danjulio/gCore/Firmware/gcore_ctrl/src/adc.c

/*
 * adc.c
 *
 * ADC Measurement module
 *  Implement an interrupt-driven sampling system for USB input voltage and current, battery
 *  voltage, load current and internal temp.  TIMER0 IRQ triggers ADC readings.  ADC IRQ used
 *  to update values.
 *
 * Functions:
 *  1. Initialization
 *    - Initialize filter used for noisy voltage and current measurements
 *    - Read temp - initialize averaging array
 *    - Enable timer + adc interrupts
 *  2. Digitally filtered measurements for voltage and current to handle varying values that
 *     make it through the external low-pass hardware filters.  Measurements made for each
 *     voltage and current channel at approximately 1 kHz.
 *  3. Skew TIMER0 reload value back and forth around the center sample rate to jitter ADC sampling.
 *  4. Temperature sensor measurements every second and averaging over a several second period.
 *  5. Value access routines for other modules.
 *
 * Copyright (c) 2021-2022 danjuliodesigns, LLC.  All rights reserved.
 *
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
 */
#include "intrins.h"
#include "adc.h"
#include "config.h"
#include "smbus.h"


//-----------------------------------------------------------------------------
// Module constants
//-----------------------------------------------------------------------------

// ADC Inputs
#define _ADC_VU_CH 1
#define _ADC_IU_CH 2
#define _ADC_VB_CH 3
#define _ADC_IL_CH 4
#define _ADC_TI_CH 27

// Timer0 reload min/max counts
//  Chosen to allow the sample point to skew around the entire PWM period to
//  more accurately measure a varying signal during that time.
//    - Skew around timer 0 reload base value of 0x80 (~250 uSec/sample)
//    - Timer 0 count = 1.96 uSec
//    - PWM Period = 41.8 uSec
//    => Minimum of 41.8/1.96 = ~21.3 counts
//  However the following values were empirically found to work well with
//  the selected filter constant K.
#define _ADC_TH0_MIN 0x77
#define _ADC_TH0_MAX 0x88



//-----------------------------------------------------------------------------
// Voltage and Current ADC Count to output lookup tables
//-----------------------------------------------------------------------------

// mV = (ADC_COUNT * VREF * V_SF) / 1023 = (ADC_COUNT * 1250 * 5.02) / 1023
code const uint16_t adc_2_mv[] = {
	0, 6, 12, 18, 25, 31, 37, 43, 49, 55, 61, 67, 74, 80, 86, 92,
	98, 104, 110, 117, 123, 129, 135, 141, 147, 153, 159, 166, 172, 178, 184, 190,
	196, 202, 209, 215, 221, 227, 233, 239, 245, 251, 258, 264, 270, 276, 282, 288,
	294, 301, 307, 313, 319, 325, 331, 337, 343, 350, 356, 362, 368, 374, 380, 386,
	393, 399, 405, 411, 417, 423, 429, 436, 442, 448, 454, 460, 466, 472, 478, 485,
	491, 497, 503, 509, 515, 521, 528, 534, 540, 546, 552, 558, 564, 570, 577, 583,
	589, 595, 601, 607, 613, 620, 626, 632, 638, 644, 650, 656, 662, 669, 675, 681,
	687, 693, 699, 705, 712, 718, 724, 730, 736, 742, 748, 754, 761, 767, 773, 779,
	785, 791, 797, 804, 810, 816, 822, 828, 834, 840, 846, 853, 859, 865, 871, 877,
	883, 889, 896, 902, 908, 914, 920, 926, 932, 938, 945, 951, 957, 963, 969, 975,
	981, 988, 994, 1000, 1006, 1012, 1018, 1024, 1030, 1037, 1043, 1049, 1055, 1061, 1067, 1073,
	1080, 1086, 1092, 1098, 1104, 1110, 1116, 1123, 1129, 1135, 1141, 1147, 1153, 1159, 1165, 1172,
	1178, 1184, 1190, 1196, 1202, 1208, 1215, 1221, 1227, 1233, 1239, 1245, 1251, 1257, 1264, 1270,
	1276, 1282, 1288, 1294, 1300, 1307, 1313, 1319, 1325, 1331, 1337, 1343, 1349, 1356, 1362, 1368,
	1374, 1380, 1386, 1392, 1399, 1405, 1411, 1417, 1423, 1429, 1435, 1441, 1448, 1454, 1460, 1466,
	1472, 1478, 1484, 1491, 1497, 1503, 1509, 1515, 1521, 1527, 1533, 1540, 1546, 1552, 1558, 1564,
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
	430, 431, 433, 434, 435, 436, 437, 439, 440, 441, 442, 444, 445, 446, 447, 448,
	450, 451, 452, 453, 455, 456, 457, 458, 459, 461, 462, 463, 464, 466, 467, 468,
	469, 470, 472, 473, 474, 475, 477, 478, 479, 480, 481, 483, 484, 485, 486, 488,
	489, 490, 491, 492, 494, 495, 496, 497, 499, 500, 501, 502, 503, 505, 506, 507,
	508, 510, 511, 512, 513, 514, 516, 517, 518, 519, 521, 522, 523, 524, 525, 527,
	528, 529, 530, 532, 533, 534, 535, 536, 538, 539, 540, 541, 543, 544, 545, 546,
	547, 549, 550, 551, 552, 554, 555, 556, 557, 558, 560, 561, 562, 563, 565, 566,
	567, 568, 569, 571, 572, 573, 574, 576, 577, 578, 579, 580, 582, 583, 584, 585,
	587, 588, 589, 590, 591, 593, 594, 595, 596, 598, 599, 600, 601, 602, 604, 605,
	606, 607, 609, 610, 611, 612, 613, 615, 616, 617, 618, 620, 621, 622, 623, 624,
	626, 627, 628, 629, 630, 632, 633, 634, 635, 637, 638, 639, 640, 641, 643, 644,
	645, 646, 648, 649, 650, 651, 652, 654, 655, 656, 657, 659, 660, 661, 662, 663,
	665, 666, 667, 668, 670, 671, 672, 673, 674, 676, 677, 678, 679, 681, 682, 683,
	684, 685, 687, 688, 689, 690, 692, 693, 694, 695, 696, 698, 699, 700, 701, 703,
	704, 705, 706, 707, 709, 710, 711, 712, 714, 715, 716, 717, 718, 720, 721, 722,
	723, 725, 726, 727, 728, 729, 731, 732, 733, 734, 736, 737, 738, 739, 740, 742,
	743, 744, 745, 747, 748, 749, 750, 751, 753, 754, 755, 756, 758, 759, 760, 761,
	762, 764, 765, 766, 767, 769, 770, 771, 772, 773, 775, 776, 777, 778, 780, 781,
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
};




//-----------------------------------------------------------------------------
// Variables
//-----------------------------------------------------------------------------

// Filtered measurement variables
static volatile uint32_t SI_SEG_IDATA adcFilterSum[4];

// Temperature measurement variables
static volatile uint16_t SI_SEG_IDATA adcTempAvgArray[ADC_NUM_TEMP_SMPLS];
static volatile uint8_t SI_SEG_IDATA adcTempAvgIndex;

// State management variables
static volatile uint8_t adcMeasIndex;	     // Current index being measured
static volatile uint8_t adcStoredMeasIndex;  // Index to restore after temperature measurement "interruption"
static volatile uint16_t adcTempMeasCount;	 // Counts down series between temperature measurements (slow)

// Timer 0 sample control
static volatile uint8_t adcTimer0Reload;
static volatile bit adcTimer0ReloadInc;



//-----------------------------------------------------------------------------
// Forward declarations for internal functions
//-----------------------------------------------------------------------------
static void _ADC_DelayMsec(uint8_t mSec);
static uint16_t _ADC_GetSingleReading(uint8_t adcChannel);
static void _ADC_PushFilteredVal(uint16_t val, uint8_t index);
static void _ADC_PushTemp(uint16_t val);
static int16_t _adc2IntT10(uint16_t adcVal);



//-----------------------------------------------------------------------------
// API Routines
//-----------------------------------------------------------------------------
void ADC_Init()
{
	uint8_t i;
	uint16_t v;

	// Make sure ADC Interrupts are disabled so ISRs don't fire while we're initializing
	ADC_DIS_INT();

	// Delay to allow voltages to stabilize
	_ADC_DelayMsec(50);

	// Initialize variables
	adcMeasIndex = 0;
	adcTempMeasCount = ADC_TEMP_EVAL_COUNT;
	adcTimer0Reload = 0x80;
	adcTimer0ReloadInc = 1;

	// Setup the filtered ADC value filters
	v = _ADC_GetSingleReading(_ADC_VU_CH);
	adcFilterSum[ADC_MEAS_VU_INDEX] = (v << ADC_V_FILTER_SHIFT);
	SMB_SetVU(adc_2_mv[v]);
	v = _ADC_GetSingleReading(_ADC_IU_CH);
	adcFilterSum[ADC_MEAS_IU_INDEX] = (v << ADC_I_FILTER_SHIFT);
	SMB_SetIU(adc_2_ma[v]);
	v = _ADC_GetSingleReading(_ADC_VB_CH);
	adcFilterSum[ADC_MEAS_VB_INDEX] = (v << ADC_V_FILTER_SHIFT);
	SMB_SetVB(adc_2_mv[v]);
	v = _ADC_GetSingleReading(_ADC_IL_CH);
	adcFilterSum[ADC_MEAS_IL_INDEX] = (v << ADC_I_FILTER_SHIFT);
	SMB_SetIL(adc_2_ma[v]);

	// Load the temperature averaging arrays
	v = _ADC_GetSingleReading(_ADC_TI_CH);
	for (i=0; i<ADC_NUM_TEMP_SMPLS-1; i++) {
		_ADC_PushTemp(v);
	}

	// Configure the ADC input for the initial reading
	ADC0MX = _ADC_VU_CH;

	// Enable Timer0
	TCON_TR0 = 1;

	// Enable ADC Interrupts
	ADC_EN_INT();
}



//-----------------------------------------------------------------------------
// Interrupt Handlers
//-----------------------------------------------------------------------------
// TIMER0_IRQ requires ~1.3 - 1.5 uSec typically
SI_INTERRUPT (TIMER0_ISR, TIMER0_IRQn)
{
	// Trigger an ADC reading
	ADC0CN0_ADBUSY = 1;

	// Update the reload value to skew the period between samples
	if (adcTimer0ReloadInc == 1) {
		if (++adcTimer0Reload == _ADC_TH0_MAX) {
			adcTimer0ReloadInc = 0;
		}
	} else {
		if (--adcTimer0Reload == _ADC_TH0_MIN) {
			adcTimer0ReloadInc = 1;
		}
	}
	TH0 = adcTimer0Reload;

	// Clear TCON::TF0 (Timer 0 Overflow Flag) - done by HW on entry to ISR
}


// ADC0E0C_IRQ requires ~22-27 uSec
// (greater if blocked while writing to SMBus, typ up to 400 uSec if reading time)
SI_INTERRUPT (ADC0EOC_ISR, ADC0EOC_IRQn)
{
	// Store the ADC result
	if (adcMeasIndex <= ADC_MEAS_IL_INDEX) {
		_ADC_PushFilteredVal(ADC0, adcMeasIndex);
	} else {
		// Temperature
		_ADC_PushTemp(ADC0);
	}

	// Setup the next ADC reading
	if (adcMeasIndex == ADC_MEAS_T_INDEX) {
		// Restore normal operation
		adcMeasIndex = adcStoredMeasIndex;
	} else {
		// Setup for next channel
		if (++adcMeasIndex > ADC_MEAS_IL_INDEX) {
			adcMeasIndex = 0;
		}
		if (--adcTempMeasCount == 0) {
			// Setup special case of occasional temperature measurement
			adcTempMeasCount = ADC_TEMP_EVAL_COUNT; // Reset temperature timer
			adcStoredMeasIndex = adcMeasIndex;      // Save current normal channel to restore
			adcMeasIndex = ADC_MEAS_T_INDEX;        // Internal temperature sensor
		}
	}

	// Configure the ADC input for the next reading
	switch (adcMeasIndex) {
	case ADC_MEAS_VU_INDEX:
		ADC0MX = _ADC_VU_CH;
		break;
	case ADC_MEAS_IU_INDEX:
		ADC0MX = _ADC_IU_CH;
		break;
	case ADC_MEAS_VB_INDEX:
		ADC0MX = _ADC_VB_CH;
		break;
	case ADC_MEAS_IL_INDEX:
		ADC0MX = _ADC_IL_CH;
		break;
	default:
		ADC0MX = _ADC_TI_CH;
		break;
	}

	// Clear ADC0CN0::ADINT (Conversion Complete Interrupt Flag)
	ADC0CN0_ADINT = 0;
}



//-----------------------------------------------------------------------------
// Internal Routines
//-----------------------------------------------------------------------------

// Delay function designed for use during initialization - ADC/Timer0 interrupts must be disabled
void _ADC_DelayMsec(uint8_t mSec)
{
	uint8_t i;

	// Uses Timer0 overflow at ~250 uSec
	TCON_TF0 = 0;  // Clear overflow flag
	TL0 = TH0;     // Manually set timer for first time
	TCON_TR0 = 1;  // Enable Timer 0
	while (mSec--) {
		for (i=0; i<4; i++) {
			// Spin until timer overflows
			while (TCON_TF0 != 1) {};

			// Reset for next period
			TCON_TF0 = 0;
		}
	}

	// Disable Timer 0
	TCON_TR0 = 0;
	TCON_TF0 = 0;
}


// Single ADC measurement - ADC Interrupts must be disabled
uint16_t _ADC_GetSingleReading(uint8_t adcChannel)
{
	// Set the ADC Channel
	ADC0MX = adcChannel;

	// Wait >5 uSec for input to settle
	_ADC_DelayMsec(10);

	// Trigger ADC
	ADC0CN0_ADINT = 0;
	ADC0CN0_ADBUSY = 1;

	// Wait for ADC to finish
	while (ADC0CN0_ADINT != 1) {};
	ADC0CN0_ADINT = 0;

	return(ADC0);
}


void _ADC_PushFilteredVal(uint16_t val, uint8_t index)
{
	uint16_t v;

	// Even indices are voltage, odd are current
	if (index & 0x01) {
		// Update current filter with current sample
		adcFilterSum[index] = adcFilterSum[index] - (adcFilterSum[index] >> ADC_I_FILTER_SHIFT) + val;

		// Scale for unity gain
		v = adcFilterSum[index] >> ADC_I_FILTER_SHIFT;

		// Push value into SMBUS register
		if (index & 0x02) {
			SMB_SetIL(adc_2_ma[v]);
		} else {
			SMB_SetIU(adc_2_ma[v]);
		}
	} else {
		// Update current filter with current sample
		adcFilterSum[index] = adcFilterSum[index] - (adcFilterSum[index] >> ADC_V_FILTER_SHIFT) + val;

		// Scale for unity gain
		v = adcFilterSum[index] >> ADC_V_FILTER_SHIFT;

		// Push value into SMBUS register
		if (index & 0x02) {
			SMB_SetVB(adc_2_mv[v]);
		} else {
			SMB_SetVU(adc_2_mv[v]);
		}
	}
}


void _ADC_PushTemp(uint16_t val)
{
	uint8_t i;
	uint16_t tempAvgAdcVal = 0;

	// Push current value
	adcTempAvgArray[adcTempAvgIndex] = val;
	if (++adcTempAvgIndex == ADC_NUM_TEMP_SMPLS) adcTempAvgIndex = 0;

	// Compute current averaged ADC value
	tempAvgAdcVal = 0;
	for (i=0; i<ADC_NUM_TEMP_SMPLS; i++) {
		tempAvgAdcVal += adcTempAvgArray[i];
	}

	// Round up the pre-divided value if necessary and then scale to divide
	if (tempAvgAdcVal & ADC_TEMP_RND_MASK) {
		// Round up unshifted sum
		tempAvgAdcVal += ADC_TEMP_RND_MASK;
	}
	tempAvgAdcVal = tempAvgAdcVal >> ADC_TEMP_SHIFT;

	// Push value into SMBUS
	SMB_SetTemp(_adc2IntT10(tempAvgAdcVal));
}


// Return temp in units of C * 10
//
// Internal Temperature Sensor spec says slope is 3.4 mV/C and a 10-bit
// measurement for each device is held in the TOFF register (measured
// at 25C).  An offset for 0C can be calculated by subtracting the
// computed ADC count for 25 degrees C from the TOFF register and
// scaling to 10-bits.
int16_t _adc2IntT10(uint16_t adcVal)
{
	int32_t t;

	// Offset for 0-degree with internal calibration offset
	//   - Offset @ 0C is 940 mV nominal (10-bit ADC count = (940/ADC_VREF_MV)*1023 = 769 ideal
	//   - {TOFFH[7:0], TOFFL[7:6]} contain 10-bit calibrated offset voltage
	//   - Adjust ADC count to 0-degrees with calibration: adcVal - 769 - TOFF
	//
	//t = 961620 / ADC_VREF_MV;
	//t = (int32_t) adcVal - t;
	t = (int32_t) adcVal - 769;
	t = t - (((int32_t) TOFFH << 2) | ((int32_t) TOFFL >> 6));

	// Compute temperature
	//   T_C_10 = (100*ADC_CAL_MV*ADC_VREF_MV)/(1023 * 34)
	t = t * ADC_VREF_MV * 100;
	t = t / 34782;

	return (t);
}
