danjulio/gCore/Arduino/gCore/src/gCore_ILI9488.h

/*
 * Adafruit GFX compatible LCD driver library for danjuliodesigns, LLC gCore
 * development board. Supports 16-bit colors natively.
 *
 * You must also include the Adafruit_GFX library that can be downloaded
 * from https://github/adafruit/Adafruit_GFX.  Thanks to Limor Fried/Ladyada 
 * at Adafruit Industries for all her hard work on these libraries.
 *
 * Written by Dan Julio
 *
 * Copyright 2021 danjuliodesigns, LLC
 *
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
 *
 * The original Adafruit ILI9488 library had the following header which is being
 * included below:
 *
 *  This is our library for the Adafruit  ILI9488 Breakout and Shield
 * ----> http://www.adafruit.com/products/1651
 *
 *  Check out the links above for our tutorials and wiring diagrams
 * These displays use SPI to communicate, 4 or 5 pins are required to
 * interface (RST is optional)
 * Adafruit invests time and resources providing this open source code,
 * please support Adafruit and open-source hardware by purchasing
 * products from Adafruit!
 *
 * Written by Limor Fried/Ladyada for Adafruit Industries.
 * MIT license, all text above must be included in any redistribution
 */
#ifndef _GCORE_ILI9488_
#define _GCORE_ILI9488_

#include <Arduino.h>
#include "Adafruit_GFX.h"
#include <SPI.h>
#include "esp_system.h"


/*
 * You'll probably need to change the SPI frequency to a lower value
 * if you're using this driver on hardware without a serial-to-parallel
 * converter like gCore has.
 */
#define ILI9488_SPI_MHZ                             80*1000*1000


/*
 * LCD resolution
 */
#define ILI9488_TFTWIDTH                            320
#define ILI9488_TFTHEIGHT                           480


/*
 * ILI9488 Registers
 */

// Level 1 Commands (from the display Datasheet)
#define ILI9488_CMD_NOP                             0x00
#define ILI9488_CMD_SOFTWARE_RESET                  0x01
#define ILI9488_CMD_READ_DISP_ID                    0x04
#define ILI9488_CMD_READ_ERROR_DSI                  0x05
#define ILI9488_CMD_READ_DISP_STATUS                0x09
#define ILI9488_CMD_READ_DISP_POWER_MODE            0x0A
#define ILI9488_CMD_READ_DISP_MADCTRL               0x0B
#define ILI9488_CMD_READ_DISP_PIXEL_FORMAT          0x0C
#define ILI9488_CMD_READ_DISP_IMAGE_MODE            0x0D
#define ILI9488_CMD_READ_DISP_SIGNAL_MODE           0x0E
#define ILI9488_CMD_READ_DISP_SELF_DIAGNOSTIC       0x0F
#define ILI9488_CMD_ENTER_SLEEP_MODE                0x10
#define ILI9488_CMD_SLEEP_OUT                       0x11
#define ILI9488_CMD_PARTIAL_MODE_ON                 0x12
#define ILI9488_CMD_NORMAL_DISP_MODE_ON             0x13
#define ILI9488_CMD_DISP_INVERSION_OFF              0x20
#define ILI9488_CMD_DISP_INVERSION_ON               0x21
#define ILI9488_CMD_PIXEL_OFF                       0x22
#define ILI9488_CMD_PIXEL_ON                        0x23
#define ILI9488_CMD_DISPLAY_OFF                     0x28
#define ILI9488_CMD_DISPLAY_ON                      0x29
#define ILI9488_CMD_COLUMN_ADDRESS_SET              0x2A
#define ILI9488_CMD_PAGE_ADDRESS_SET                0x2B
#define ILI9488_CMD_MEMORY_WRITE                    0x2C
#define ILI9488_CMD_MEMORY_READ                     0x2E
#define ILI9488_CMD_PARTIAL_AREA                    0x30
#define ILI9488_CMD_VERT_SCROLL_DEFINITION          0x33
#define ILI9488_CMD_TEARING_EFFECT_LINE_OFF         0x34
#define ILI9488_CMD_TEARING_EFFECT_LINE_ON          0x35
#define ILI9488_CMD_MEMORY_ACCESS_CONTROL           0x36
#define ILI9488_CMD_VERT_SCROLL_START_ADDRESS       0x37
#define ILI9488_CMD_IDLE_MODE_OFF                   0x38
#define ILI9488_CMD_IDLE_MODE_ON                    0x39
#define ILI9488_CMD_COLMOD_PIXEL_FORMAT_SET         0x3A
#define ILI9488_CMD_WRITE_MEMORY_CONTINUE           0x3C
#define ILI9488_CMD_READ_MEMORY_CONTINUE            0x3E
#define ILI9488_CMD_SET_TEAR_SCANLINE               0x44
#define ILI9488_CMD_GET_SCANLINE                    0x45
#define ILI9488_CMD_WRITE_DISPLAY_BRIGHTNESS        0x51
#define ILI9488_CMD_READ_DISPLAY_BRIGHTNESS         0x52
#define ILI9488_CMD_WRITE_CTRL_DISPLAY              0x53
#define ILI9488_CMD_READ_CTRL_DISPLAY               0x54
#define ILI9488_CMD_WRITE_CONTENT_ADAPT_BRIGHTNESS  0x55
#define ILI9488_CMD_READ_CONTENT_ADAPT_BRIGHTNESS   0x56
#define ILI9488_CMD_WRITE_MIN_CAB_LEVEL             0x5E
#define ILI9488_CMD_READ_MIN_CAB_LEVEL              0x5F
#define ILI9488_CMD_READ_ABC_SELF_DIAG_RES          0x68
#define ILI9488_CMD_READ_ID1                        0xDA
#define ILI9488_CMD_READ_ID2                        0xDB
#define ILI9488_CMD_READ_ID3                        0xDC

/* Level 2 Commands (from the display Datasheet) */
#define ILI9488_CMD_INTERFACE_MODE_CONTROL          0xB0
#define ILI9488_CMD_FRAME_RATE_CONTROL_NORMAL       0xB1
#define ILI9488_CMD_FRAME_RATE_CONTROL_IDLE_8COLOR  0xB2
#define ILI9488_CMD_FRAME_RATE_CONTROL_PARTIAL      0xB3
#define ILI9488_CMD_DISPLAY_INVERSION_CONTROL       0xB4
#define ILI9488_CMD_BLANKING_PORCH_CONTROL          0xB5
#define ILI9488_CMD_DISPLAY_FUNCTION_CONTROL        0xB6
#define ILI9488_CMD_ENTRY_MODE_SET                  0xB7
#define ILI9488_CMD_BACKLIGHT_CONTROL_1             0xB9
#define ILI9488_CMD_BACKLIGHT_CONTROL_2             0xBA
#define ILI9488_CMD_HS_LANES_CONTROL                0xBE
#define ILI9488_CMD_POWER_CONTROL_1                 0xC0
#define ILI9488_CMD_POWER_CONTROL_2                 0xC1
#define ILI9488_CMD_POWER_CONTROL_NORMAL_3          0xC2
#define ILI9488_CMD_POWER_CONTROL_IDEL_4            0xC3
#define ILI9488_CMD_POWER_CONTROL_PARTIAL_5         0xC4
#define ILI9488_CMD_VCOM_CONTROL_1                  0xC5
#define ILI9488_CMD_CABC_CONTROL_1                  0xC6
#define ILI9488_CMD_CABC_CONTROL_2                  0xC8
#define ILI9488_CMD_CABC_CONTROL_3                  0xC9
#define ILI9488_CMD_CABC_CONTROL_4                  0xCA
#define ILI9488_CMD_CABC_CONTROL_5                  0xCB
#define ILI9488_CMD_CABC_CONTROL_6                  0xCC
#define ILI9488_CMD_CABC_CONTROL_7                  0xCD
#define ILI9488_CMD_CABC_CONTROL_8                  0xCE
#define ILI9488_CMD_CABC_CONTROL_9                  0xCF
#define ILI9488_CMD_NVMEM_WRITE                     0xD0
#define ILI9488_CMD_NVMEM_PROTECTION_KEY            0xD1
#define ILI9488_CMD_NVMEM_STATUS_READ               0xD2
#define ILI9488_CMD_READ_ID4                        0xD3
#define ILI9488_CMD_ADJUST_CONTROL_1                0xD7
#define ILI9488_CMD_READ_ID_VERSION                 0xD8
#define ILI9488_CMD_POSITIVE_GAMMA_CORRECTION       0xE0
#define ILI9488_CMD_NEGATIVE_GAMMA_CORRECTION       0xE1
#define ILI9488_CMD_DIGITAL_GAMMA_CONTROL_1         0xE2
#define ILI9488_CMD_DIGITAL_GAMMA_CONTROL_2         0xE3
#define ILI9488_CMD_SET_IMAGE_FUNCTION              0xE9
#define ILI9488_CMD_ADJUST_CONTROL_2                0xF2
#define ILI9488_CMD_ADJUST_CONTROL_3                0xF7
#define ILI9488_CMD_ADJUST_CONTROL_4                0xF8
#define ILI9488_CMD_ADJUST_CONTROL_5                0xF9
#define ILI9488_CMD_SPI_READ_SETTINGS               0xFB
#define ILI9488_CMD_ADJUST_CONTROL_6                0xFC
#define ILI9488_CMD_ADJUST_CONTROL_7                0xFF


/*
 * Color definitions
 */
#define ILI9488_BLACK       0x0000      /*   0,   0,   0 */
#define ILI9488_NAVY        0x000F      /*   0,   0, 128 */
#define ILI9488_DARKGREEN   0x03E0      /*   0, 128,   0 */
#define ILI9488_DARKCYAN    0x03EF      /*   0, 128, 128 */
#define ILI9488_MAROON      0x7800      /* 128,   0,   0 */
#define ILI9488_PURPLE      0x780F      /* 128,   0, 128 */
#define ILI9488_OLIVE       0x7BE0      /* 128, 128,   0 */
#define ILI9488_LIGHTGREY   0xC618      /* 192, 192, 192 */
#define ILI9488_DARKGREY    0x7BEF      /* 128, 128, 128 */
#define ILI9488_BLUE        0x001F      /*   0,   0, 255 */
#define ILI9488_GREEN       0x07E0      /*   0, 255,   0 */
#define ILI9488_CYAN        0x07FF      /*   0, 255, 255 */
#define ILI9488_RED         0xF800      /* 255,   0,   0 */
#define ILI9488_MAGENTA     0xF81F      /* 255,   0, 255 */
#define ILI9488_YELLOW      0xFFE0      /* 255, 255,   0 */
#define ILI9488_WHITE       0xFFFF      /* 255, 255, 255 */
#define ILI9488_ORANGE      0xFD20      /* 255, 165,   0 */
#define ILI9488_GREENYELLOW 0xAFE5      /* 173, 255,  47 */
#define ILI9488_PINK        0xF81F


/*
 * MADCTL masks
 */
#define ILI9488_MADCTL_MY   0x80
#define ILI9488_MADCTL_MX   0x40
#define ILI9488_MADCTL_MV   0x20
#define ILI9488_MADCTL_ML   0x10
#define ILI9488_MADCTL_RGB  0x00
#define ILI9488_MADCTL_BGR  0x08
#define ILI9488_MADCTL_MH   0x04



/*
 * Class definition
 */
class gCore_ILI9488 : public Adafruit_GFX {

	public:
		gCore_ILI9488();
		gCore_ILI9488(int8_t _CS, int8_t _DC, int8_t _MOSI, int8_t _SCLK, int8_t _RST = -1);

		void	begin(void),
				setAddrWindow(uint16_t x0, uint16_t y0, uint16_t x1, uint16_t y1),
				drawImage(const uint8_t* img, uint16_t x, uint16_t y, uint16_t w, uint16_t h),
				fillScreen(uint16_t color),
				drawPixel(int16_t x, int16_t y, uint16_t color),
				drawFastVLine(int16_t x, int16_t y, int16_t h, uint16_t color),
				drawFastHLine(int16_t x, int16_t y, int16_t w, uint16_t color),
				fillRect(int16_t x, int16_t y, int16_t w, int16_t h, uint16_t color),
				writePixel(int16_t x, int16_t y, uint16_t color),
				pushPixels(const void* data, int32_t len),
				setRotation(uint8_t r),
				invertDisplay(boolean i);
		
		uint16_t color565(uint8_t r, uint8_t g, uint8_t b);

	private:
		// Methods
		void sendLcdCommand(uint8_t cmd);
		void sendLcdCommandData(uint8_t* data, uint8_t len);
		void sendLcdPixelColor(uint16_t color);
		void sendLcdPixelsColor(uint16_t color, int32_t len);
		void sendLcdImageData(uint8_t* data, int32_t len);
		
		// Pin Variables
		int _dc, _rst, _sclk, _mosi, _csn;
		
		// Set Address buffers
		uint8_t xb[4], yb[4];
		
		// Arduino SPI library
		SPIClass* spi;
};


#endif /* _GCORE_ILI9488_ */
