danjulio/gCore/Arduino/gCore/examples/joystick_3d/naruto.h

// 3D model [naruto]
//
// - vertices   : 1326
// - textures   : 1145
// - normals    : 1596
// - triangles  : 2472
//
// - memory size: 61kb
//
// - model bounding box: [-0.8,0.8]x[-1.0,1.0]x[-0.2,0.2]
//
// object [naruto_1] (tagged [ | g Body.bmp | usemtl Body.bmp]) with 2166 triangles (250 chains)
// object [naruto_2] (tagged [g Head.bmp | usemtl Head.bmp]) with 298 triangles (45 chains)
// object [naruto_3] (tagged [g Eye.bmp | usemtl Eye.bmp]) with 8 triangles (3 chains)

#pragma once

#include <tgx.h>

#include "naruto_body_texture.h" // texture for object [naruto_1]

#include "naruto_head_texture.h" // texture for object [naruto_2]

#include "naruto_eye_texture.h" // texture for object [naruto_3]


// vertex array: 15kb.
const tgx::fVec3 naruto_vert_array[1326] PROGMEM = {
{0.47319183483182337,0.24162330723210745,-0.050456744970095564},
{0.4671941603889574,0.30364920723943234,0.013004932488957503},
{0.3714407644208081,0.23958925801550482,-0.0683600275339623},
{0.3968299224426658,0.3065881425004072,0.009901397708671501},
{0.4719055505373434,0.37807414000583855,0.00044870382365581847},
{0.402595766576643,0.38223960716877653,-0.009714437782148226},
{0.47877071903927726,0.3950426229370888,-0.09203663262886708},
{0.3936665604858923,0.40913932661297153,-0.1135893729584677},
{0.4869520854239348,0.34634337606028254,-0.13639100559724365},
{0.39268689047091054,0.34673958153657064,-0.15632093376462247},
{0.3906976368527031,0.27868616828210646,-0.13631622162663437},
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
4, // chain 0
1314,1139,1584, 1315,1140,1585, 1316,1141,1586, 
34085,1142,1587, 34086,1143,1588, 1319,1144,1589, 
3, // chain 1
1320,1141,1590, 1321,1142,1591, 1322,1140,1592, 
34091,1143,1593, 34092,1144,1594, 
1, // chain 2
1320,1141,1590, 1322,1140,1592, 1325,1139,1595, 

 0};


// mesh info for object naruto_3 (with tag [g Eye.bmp | usemtl Eye.bmp])
const tgx::Mesh3D<tgx::RGB565> naruto_3 = 
    {
    1, // version/id
    
    1326, // number of vertices
    1145, // number of texture coords
    1596, // number of normal vectors
    8, // number of triangles
    46, 
    
    naruto_vert_array, // array of vertices
    naruto_tex_array, // array of texture coords
    naruto_norm_array, // array of normal vectors        
    naruto_3_face, // array of face vertex indexes   
    
    &naruto_eye_texture, // pointer to texture image 
    
    { 0.75f , 0.75f, 0.75f }, // default color
    
    0.1f, // ambiant light strength 
    0.7f, // diffuse light strength
    0.6f, // specular light strength
    32, // specular exponent
    
    nullptr, // next mesh to draw after this one    
    
    { // mesh bounding box
    -0.09621331738739658, 0.09630305815212771, 
    0.6607052001295709, 0.7343748895767935, 
    0.07790246218370915, 0.1210752484164588
    },
    
    "naruto" // model name    
    };
    

// mesh info for object naruto_2 (with tag [g Head.bmp | usemtl Head.bmp])
const tgx::Mesh3D<tgx::RGB565> naruto_2 = 
    {
    1, // version/id
    
    1326, // number of vertices
    1145, // number of texture coords
    1596, // number of normal vectors
    298, // number of triangles
    1210, 
    
    naruto_vert_array, // array of vertices
    naruto_tex_array, // array of texture coords
    naruto_norm_array, // array of normal vectors        
    naruto_2_face, // array of face vertex indexes   
    
    &naruto_head_texture, // pointer to texture image 
    
    { 0.75f , 0.75f, 0.75f }, // default color
    
    0.1f, // ambiant light strength 
    0.7f, // diffuse light strength
    0.6f, // specular light strength
    32, // specular exponent
    
    &naruto_3, // next mesh to draw after this one    
    
    { // mesh bounding box
    -0.11356319856875448, 0.11378007208352141, 
    0.5534724646728937, 0.727075899261355, 
    0.008390761502363614, 0.15907298388304478
    },
    
    "naruto" // model name    
    };
    

// mesh info for object naruto_1 (with tag [ | g Body.bmp | usemtl Body.bmp])
const tgx::Mesh3D<tgx::RGB565> naruto_1 = 
    {
    1, // version/id
    
    1326, // number of vertices
    1145, // number of texture coords
    1596, // number of normal vectors
    2166, // number of triangles
    8249, 
    
    naruto_vert_array, // array of vertices
    naruto_tex_array, // array of texture coords
    naruto_norm_array, // array of normal vectors        
    naruto_1_face, // array of face vertex indexes   
    
    &naruto_body_texture, // pointer to texture image 
    
    { 0.75f , 0.75f, 0.75f }, // default color
    
    0.1f, // ambiant light strength 
    0.7f, // diffuse light strength
    0.6f, // specular light strength
    32, // specular exponent
    
    &naruto_2, // next mesh to draw after this one    
    
    { // mesh bounding box
    -0.8020693023803476, 0.8020693023803476, 
    -1.0, 1.0, 
    -0.195223555275581, 0.195223555275581
    },
    
    "naruto" // model name    
    };
    
                
/** end of naruto.h */
    
    
    
