danjulio/gCore/Arduino/gCore/examples/joystick_3d/naruto_body_texture.h

//
// texture [naruto_body]
//
#pragma once

#include <tgx.h>

const uint16_t naruto_body_texture_data[256*256] PROGMEM = {
0x0, 0x0, 0x0, 0x0, 0x0, 0x0, 0x0, 0x0, 0x0, 0x0, 0x0, 0x0, 0x0, 0x0, 0x0, 0x0, 
0x0, 0x0, 0x0, 0x0, 0x0, 0x0, 0x0, 0x0, 0x0, 0x0, 0x0, 0x0, 0x0, 0x0, 0x0, 0x0, 
0x0, 0x0, 0x0, 0x0, 0x0, 0x0, 0x0, 0x0, 0x0, 0x0, 0x0, 0x0, 0x0, 0x0, 0x0, 0x0, 
0x0, 0x0, 0x0, 0x0, 0x0, 0x0, 0x0, 0x0, 0x0, 0x0, 0x0, 0x0, 0x0, 0x0, 0x0, 0x0, 
0x0, 0x0, 0x0, 0x0, 0x0, 0x0, 0x0, 0x0, 0x0, 0x0, 0x0, 0x0, 0x0, 0x0, 0x0, 0x0, 
0x0, 0x0, 0x0, 0x0, 0x0, 0x0, 0x0, 0x0, 0x0, 0x0, 0x0, 0x0, 0x0, 0x0, 0x0, 0x0, 
0x0, 0x0, 0x0, 0x0, 0x0, 0x0, 0x0, 0x0, 0x0, 0x0, 0x0, 0x0, 0x0, 0x0, 0x0, 0x0, 
0x0, 0x0, 0x0, 0x0, 0x0, 0x0, 0x0, 0x0, 0x0, 0x0, 0x0, 0x0, 0x0, 0x0, 0x0, 0x0, 
0x0, 0x0, 0x0, 0x0, 0x0, 0x0, 0x0, 0x0, 0x0, 0x0, 0x0, 0x0, 0x0, 0x0, 0x0, 0x0, 
0x0, 0x0, 0x0, 0x0, 0x0, 0x0, 0x0, 0x0, 0x0, 0x0, 0x820, 0x820, 0x820, 0x820, 0x800, 0x0, 
0x0, 0x1040, 0x1040, 0x1860, 0x1861, 0x1861, 0x2061, 0x2061, 0x2061, 0x2061, 0x2060, 0x2061, 0x2060, 0x2081, 0x2081, 0x2081, 
0x2081, 0x2081, 0x2061, 0x1860, 0x820, 0x0, 0x0, 0x0, 0x0, 0x0, 0x0, 0x0, 0x0, 0x0, 0x0, 0x0, 
0x0, 0x0, 0x0, 0x0, 0x0, 0x0, 0x0, 0x0, 0x0, 0x0, 0x0, 0x0, 0x0, 0x0, 0x0, 0x0, 
0x0, 0x0, 0x0, 0x800, 0x1020, 0x2061, 0x2041, 0x2861, 0x821, 0x821, 0x841, 0x820, 0x0, 0x0, 0x0, 0x0, 
0x0, 0x0, 0x0, 0x0, 0x0, 0x0, 0x0, 0x0, 0x0, 0x0, 0x0, 0x0, 0x0, 0x0, 0x0, 0x0, 
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
0x8ac, 0x8ac, 0x8ac, 0x8ab, 0x8ab, 0x8ab, 0x8ab, 0x8ab, 0x8ab, 0x8ac, 0x8ac, 0x8ad, 0x8ad, 0x8cd, 0x8ad, 0x8ad, 
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
};

const tgx::Image<tgx::RGB565> naruto_body_texture((void*)naruto_body_texture_data, 256, 256);

/** end of file naruto_body_texture.h */
