danjulio/gCore/Arduino/gCore/examples/joystick_3d/naruto_head_texture.h

//
// texture [naruto_head]
//
#pragma once

#include <tgx.h>

const uint16_t naruto_head_texture_data[256*256] PROGMEM = {
0xedd3, 0xedd3, 0xedd3, 0xedd3, 0xedd3, 0xedd3, 0xedd3, 0xedd3, 0xedd3, 0xedd3, 0xedd3, 0xedd3, 0xedd3, 0xedd3, 0xedd3, 0xedd3, 
0xedd3, 0xedd3, 0xedd3, 0xedd3, 0xedd3, 0xedd3, 0xedd3, 0xedd3, 0xedd3, 0xedd3, 0xedd3, 0xedd3, 0xedd3, 0xedd3, 0xedd3, 0xedd3, 
0xedd3, 0xedd3, 0xedd3, 0xedd3, 0xedd3, 0xedd3, 0xedd3, 0xedd3, 0xedd3, 0xedd3, 0xedd3, 0xedd3, 0xedd3, 0xedd3, 0xedd3, 0xedd3, 
0xedd3, 0xedd3, 0xedd3, 0xedd3, 0xedd3, 0xedd3, 0xedd3, 0xedd3, 0xedd3, 0xedd3, 0xedd3, 0xedd3, 0xedd3, 0xedd3, 0xedd3, 0xedd3, 
0xedd3, 0xedd3, 0xedd3, 0xedd3, 0xedd3, 0xedd3, 0xedd3, 0xedd3, 0xedd3, 0xedd3, 0xedd3, 0xedd3, 0xedd3, 0xedd3, 0xedd3, 0xedd3, 
0xedd3, 0xedd3, 0xedd3, 0xedd3, 0xedd3, 0xedd3, 0xedd3, 0xedd3, 0xedd3, 0xedd3, 0xedd3, 0xedd3, 0xedd3, 0xedd3, 0xedd3, 0xedd3, 
0xedd3, 0xedd3, 0xedd3, 0xedd3, 0xedd3, 0xedd3, 0xedd3, 0xedd3, 0xedd3, 0xedd3, 0xedd3, 0xedd3, 0xedd3, 0xedd3, 0xedd3, 0xedd3, 
0xedd3, 0xedd3, 0xedd3, 0xedd3, 0xedd3, 0xedd3, 0xedd3, 0xedd3, 0xedd3, 0xedd3, 0xedd3, 0xedd3, 0xedd3, 0xedd3, 0xedd3, 0xedd3, 
0xedd3, 0xedd3, 0xedd3, 0xedd3, 0xedd3, 0xedd3, 0xedd3, 0xedd3, 0xedd3, 0xedd3, 0xedd3, 0xedd3, 0xedd3, 0xedd3, 0xedd3, 0xedd3, 
0xedd3, 0xedd3, 0xedd3, 0xedd3, 0xedd3, 0xedd3, 0xedd3, 0xedd3, 0xedd3, 0xedd3, 0xedd3, 0xedd3, 0xedd3, 0xedd3, 0xedd3, 0xedd3, 
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
0xedd3, 0xedd3, 0xedd3, 0xedd3, 0xedd3, 0xedd3, 0xedd3, 0xedd3, 0xedd3, 0xedd3, 0xedd3, 0xedd3, 0xedd3, 0xedd3, 0xedd3, 0xedd3, 
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
};

const tgx::Image<tgx::RGB565> naruto_head_texture((void*)naruto_head_texture_data, 256, 256);

/** end of file naruto_head_texture.h */
